danchouzhou/NuDAC/firmware/NeoPixel/main.c

/*************************************************************************//**
 * @file     main.c
 * @version  V1.00
 * @brief    A project template for M480 MCU.
 *
 * @copyright (C) 2016 Nuvoton Technology Corp. All rights reserved.
*****************************************************************************/
#include <stdio.h>
#include "NuMicro.h"
#include "NeoPixel.h"
#include "delay.h"

#define PLL_CLOCK           192000000

#define LED_PIN     PA15
#define LED_COUNT   1

void SYS_Init(void)
{
    /*---------------------------------------------------------------------------------------------------------*/
    /* Init System Clock                                                                                       */
    /*---------------------------------------------------------------------------------------------------------*/
    /* Unlock protected registers */
    SYS_UnlockReg();

    /* Set XT1_OUT(PF.2) and XT1_IN(PF.3) to input mode */
    //PF->MODE &= ~(GPIO_MODE_MODE2_Msk | GPIO_MODE_MODE3_Msk);

    /* Enable External XTAL (4~24 MHz) */
    //CLK_EnableXtalRC(CLK_PWRCTL_HXTEN_Msk);
    CLK_EnableXtalRC(CLK_PWRCTL_HIRCEN_Msk);

    /* Waiting for 12MHz clock ready */
    CLK_WaitClockReady(CLK_STATUS_HIRCSTB_Msk);

    /* Set core clock as PLL_CLOCK from PLL */
    CLK_SetCoreClock(PLL_CLOCK);
    /* Set PCLK0/PCLK1 to HCLK/2 */
    CLK->PCLKDIV = (CLK_PCLKDIV_APB0DIV_DIV2 | CLK_PCLKDIV_APB1DIV_DIV2);

    /* Enable UART clock */
    CLK_EnableModuleClock(UART0_MODULE);

    /* Select UART clock source from HXT */
    CLK_SetModuleClock(UART0_MODULE, CLK_CLKSEL1_UART0SEL_HIRC, CLK_CLKDIV0_UART0(1));

    /* Update System Core Clock */
    /* User can use SystemCoreClockUpdate() to calculate SystemCoreClock. */
    SystemCoreClockUpdate();



    /* Set GPB multi-function pins for UART0 RXD and TXD */
    SYS->GPB_MFPH &= ~(SYS_GPB_MFPH_PB12MFP_Msk | SYS_GPB_MFPH_PB13MFP_Msk);
    SYS->GPB_MFPH |= (SYS_GPB_MFPH_PB12MFP_UART0_RXD | SYS_GPB_MFPH_PB13MFP_UART0_TXD);
    /* Lock protected registers */
    SYS_LockReg();
}

/*
 * This is a template project for M480 series MCU. Users could based on this project to create their
 * own application without worry about the IAR/Keil project settings.
 *
 * This template application uses external crystal as HCLK source and configures UART0 to print out
 * "Hello World", users may need to do extra system configuration based on their system design.
 */

int main()
{
    /* Create a NeoPixel objects */
    STR_NEOPIXEL_T pixels;

    SYS_Init();
    /* Init UART to 115200-8n1 for print message */
    UART_Open(UART0, 115200);
    /* Connect UART to PC, and open a terminal tool to receive following message */
    printf("Hello World\n");

    /* Initialize NeoPixel */
    NeoPixel_begin(&pixels, LED_COUNT, &LED_PIN, NEO_GRB);

    /* Set pixel color */
    NeoPixel_setPixelColor(&pixels, 0, 12, 2, 16);

    /* Update pixels color */
    NeoPixel_show(&pixels);

    /* Got no where to go, just loop forever */
    while(1);

}

/*** (C) COPYRIGHT 2016 Nuvoton Technology Corp. ***/
