danchouzhou/NuDAC/firmware/SFG/User/audio_codec.c

/**************************************************************************//**
 * @file     codec.c
 * @brief    Audio Codec setting.
 * @version  1.0.0
 *
 * @copyright (C) 2017 Nuvoton Technology Corp. All rights reserved.
 ******************************************************************************/
#include <stdio.h>
#include "audio_codec.h"

uint8_t I2cWrite_MultiByteforNAU88L25(uint8_t chipadd,uint16_t subaddr, const uint8_t *p,uint32_t len)
{
    /* Send START */
    I2C_START(I2C0);
    I2C_WAIT_READY(I2C0);

    /* Send device address */
    I2C_SET_DATA(I2C0, chipadd);
    I2C_SET_CONTROL_REG(I2C0, I2C_CTL_SI);
    I2C_WAIT_READY(I2C0);

    /* Send register number and MSB of data */
    I2C_SET_DATA(I2C0, (uint8_t)(subaddr>>8));
    I2C_SET_CONTROL_REG(I2C0, I2C_CTL_SI);
    I2C_WAIT_READY(I2C0);

    /* Send register number and MSB of data */
    I2C_SET_DATA(I2C0, (uint8_t)(subaddr));
    I2C_SET_CONTROL_REG(I2C0, I2C_CTL_SI);
    I2C_WAIT_READY(I2C0);

    /* Send data */
    I2C_SET_DATA(I2C0, p[0]);
    I2C_SET_CONTROL_REG(I2C0, I2C_CTL_SI);
    I2C_WAIT_READY(I2C0);

    /* Send data */
    I2C_SET_DATA(I2C0, p[1]);
    I2C_SET_CONTROL_REG(I2C0, I2C_CTL_SI);
    I2C_WAIT_READY(I2C0);

    /* Send STOP */
    I2C_STOP(I2C0);

    return  0;
}


uint8_t I2C_WriteNAU88L25(uint16_t addr,uint16_t dat)
{
    uint8_t Tx_Data0[2];

    Tx_Data0[0] = (uint8_t)(dat >> 8);
    Tx_Data0[1] = (uint8_t)(dat & 0x00FF);

    return ( I2cWrite_MultiByteforNAU88L25(0x1A << 1,addr,&Tx_Data0[0],2) );
}

void NAU88L25_Reset(void)
{
    I2C_WriteNAU88L25(0,  0x1);
    I2C_WriteNAU88L25(0,  0);   // Reset all registers
    CLK_SysTickDelay(10000);

    printf("NAU88L25 Software Reset.\n");
}

void NAU88L25_Setup(void)
{
    I2C_WriteNAU88L25(0x0003,  0x8053);
    I2C_WriteNAU88L25(0x0004,  0x0001);
    I2C_WriteNAU88L25(0x0005,  0x3126);
    I2C_WriteNAU88L25(0x0006,  0x0008);
    I2C_WriteNAU88L25(0x0007,  0x0010);
    I2C_WriteNAU88L25(0x0008,  0xC000);
    I2C_WriteNAU88L25(0x0009,  0x6000);
    I2C_WriteNAU88L25(0x000A,  0xF13C);
    I2C_WriteNAU88L25(0x000C,  0x0048);
    I2C_WriteNAU88L25(0x000D,  0x0000);
    I2C_WriteNAU88L25(0x000F,  0x0000);
    I2C_WriteNAU88L25(0x0010,  0x0000);
    I2C_WriteNAU88L25(0x0011,  0x0000);
    I2C_WriteNAU88L25(0x0012,  0xFFFF);
    I2C_WriteNAU88L25(0x0013,  0x0015);
    I2C_WriteNAU88L25(0x0014,  0x0110);
    I2C_WriteNAU88L25(0x0015,  0x0000);
    I2C_WriteNAU88L25(0x0016,  0x0000);
    I2C_WriteNAU88L25(0x0017,  0x0000);
    I2C_WriteNAU88L25(0x0018,  0x0000);
    I2C_WriteNAU88L25(0x0019,  0x0000);
    I2C_WriteNAU88L25(0x001A,  0x0000);
    I2C_WriteNAU88L25(0x001B,  0x0000);
    I2C_WriteNAU88L25(0x001C,  0x0002);
    I2C_WriteNAU88L25(0x001D,  0x301a);   //301A:Master, BCLK_DIV=12.288M/8=1.536M, LRC_DIV=1.536M/32=48K
    I2C_WriteNAU88L25(0x001E,  0x0000);
    I2C_WriteNAU88L25(0x001F,  0x0000);
    I2C_WriteNAU88L25(0x0020,  0x0000);
    I2C_WriteNAU88L25(0x0021,  0x0000);
    I2C_WriteNAU88L25(0x0022,  0x0000);
    I2C_WriteNAU88L25(0x0023,  0x0000);
    I2C_WriteNAU88L25(0x0024,  0x0000);
    I2C_WriteNAU88L25(0x0025,  0x0000);
    I2C_WriteNAU88L25(0x0026,  0x0000);
    I2C_WriteNAU88L25(0x0027,  0x0000);
    I2C_WriteNAU88L25(0x0028,  0x0000);
    I2C_WriteNAU88L25(0x0029,  0x0000);
    I2C_WriteNAU88L25(0x002A,  0x0000);
    I2C_WriteNAU88L25(0x002B,  0x0012);
    I2C_WriteNAU88L25(0x002C,  0x0082);
    I2C_WriteNAU88L25(0x002D,  0x0000);
    I2C_WriteNAU88L25(0x0030,  0x00CF);
    I2C_WriteNAU88L25(0x0031,  0x0000);
    I2C_WriteNAU88L25(0x0032,  0x0000);
    I2C_WriteNAU88L25(0x0033,  0x009E);
    I2C_WriteNAU88L25(0x0034,  0x029E);
    I2C_WriteNAU88L25(0x0038,  0x1486);
    I2C_WriteNAU88L25(0x0039,  0x0F12);
    I2C_WriteNAU88L25(0x003A,  0x25FF);
    I2C_WriteNAU88L25(0x003B,  0x3457);
    I2C_WriteNAU88L25(0x0045,  0x1486);
    I2C_WriteNAU88L25(0x0046,  0x0F12);
    I2C_WriteNAU88L25(0x0047,  0x25F9);
    I2C_WriteNAU88L25(0x0048,  0x3457);
    I2C_WriteNAU88L25(0x004C,  0x0000);
    I2C_WriteNAU88L25(0x004D,  0x0000);
    I2C_WriteNAU88L25(0x004E,  0x0000);
    I2C_WriteNAU88L25(0x0050,  0x2007);
    I2C_WriteNAU88L25(0x0051,  0x0000);
    I2C_WriteNAU88L25(0x0053,  0xC201);
    I2C_WriteNAU88L25(0x0054,  0x0C95);
    I2C_WriteNAU88L25(0x0055,  0x0000);
    I2C_WriteNAU88L25(0x0058,  0x1A14);
    I2C_WriteNAU88L25(0x0059,  0x00FF);
    I2C_WriteNAU88L25(0x0066,  0x0060);
    I2C_WriteNAU88L25(0x0068,  0xC300);
    I2C_WriteNAU88L25(0x0069,  0x0000);
    I2C_WriteNAU88L25(0x006A,  0x0083);
    I2C_WriteNAU88L25(0x0071,  0x0011);
    I2C_WriteNAU88L25(0x0072,  0x0260);
    I2C_WriteNAU88L25(0x0073,  0x332C);
    I2C_WriteNAU88L25(0x0074,  0x4502);
    I2C_WriteNAU88L25(0x0076,  0x3140);
    I2C_WriteNAU88L25(0x0077,  0x0000);
    I2C_WriteNAU88L25(0x007F,  0x553F);
    I2C_WriteNAU88L25(0x0080,  0x0420);
    I2C_WriteNAU88L25(0x0001,  0x07D4);

    printf("NAU88L25 Configured done.\n");
}
