danchouzhou/NuDAC/firmware/ISP_HID_AUTO/User/targetdev.h

/***************************************************************************//**
 * @file     targetdev.h
 * @brief    ISP support function header file
 * @version  0x32
 * @date     14, June, 2017
 *
 * @note
 * Copyright (C) 2017-2018 Nuvoton Technology Corp. All rights reserved.
 ******************************************************************************/
#ifndef __TARGET_H__
#define __TARGET_H__

#ifdef __cplusplus
extern "C"
{
#endif

// Nuvoton MCU Peripheral Access Layer Header File
#include "M480.h"
#include "isp_user.h"
#define DetectPin                   PA15

#ifdef __cplusplus
}
#endif

#endif //__TARGET_H__
